STU-FEI-TP26-FAST-LIVO2/Hardware/parameters_datasheets/Hesai_XT16_coordinate_origin.png

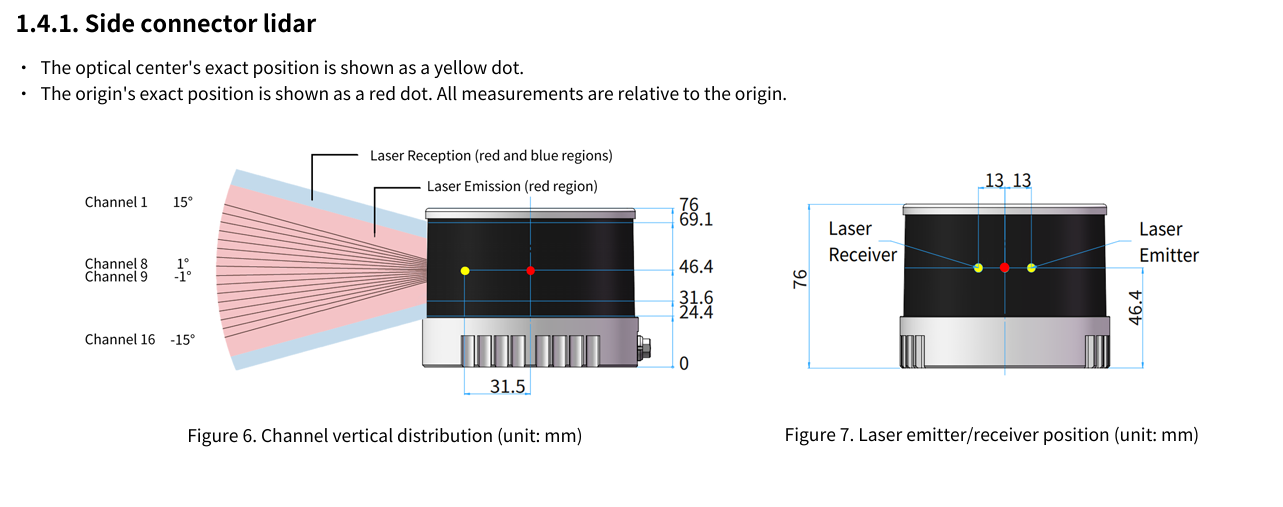
parameters_datasheets/Hesai_XT16_coordinate_origin.png
