STU-FEI-TP26-FAST-LIVO2/Hardware/parameters_datasheets/IMU_dimensions_and_origin.png

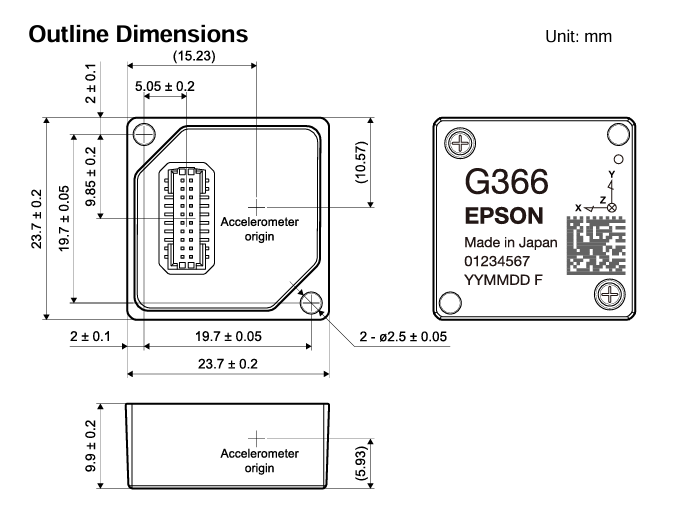
parameters_datasheets/IMU_dimensions_and_origin.png
